jboone/tedium/tedium/tools/tedium-tool/src/framer/mod.rs

use std::time::Instant;

use crate::detector::DetectionEvent;

use self::audio::TimeslotAddress;

pub mod audio;
pub mod device;
pub mod dump;
pub mod interrupt;
pub mod register;
pub mod test;
mod usb;

#[derive(Copy, Clone, Debug)]
pub enum FramerEvent {
    Interrupt { timestamp: Instant, data: [u8; usb::INTERRUPT_BYTES_MAX], length: usize },
    Digit(TimeslotAddress, DetectionEvent),
    RobbedBitState(u32, TimeslotAddress, u8),
}
